thinkexist1989/Smart-Bio-Sensor/Windows/HzBoardDataDisplay/zoomIn.png

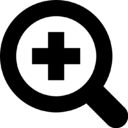
Windows/HzBoardDataDisplay/zoomIn.png
