thinkexist1989/Smart-Bio-Sensor/Firmware/Src/usart.c

/**
  ******************************************************************************
  * File Name          : USART.c
  * Description        : This file provides code for the configuration
  *                      of the USART instances.
  ******************************************************************************
  ** This notice applies to any and all portions of this file
  * that are not between comment pairs USER CODE BEGIN and
  * USER CODE END. Other portions of this file, whether 
  * inserted by the user or by software development tools
  * are owned by their respective copyright owners.
  *
  * COPYRIGHT(c) 2018 STMicroelectronics
  *
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
  ******************************************************************************
  */

/* Includes ------------------------------------------------------------------*/
#include "usart.h"

#include "gpio.h"
#include "dma.h"

/* USER CODE BEGIN 0 */
#include "dac8830.h"

extern double vout[4];
extern int valarray[4];

char RxBuf[256] = {'0'}; //0xff
char TxBuf1[256] = {'0'};
char TxBuf2[256] = {'0'};
uartCtrl uart;
BOOL bUartNewData = FALSE;

/* USER CODE END 0 */

UART_HandleTypeDef huart1;
UART_HandleTypeDef huart2;
DMA_HandleTypeDef hdma_usart1_tx;
DMA_HandleTypeDef hdma_usart2_tx;

/* USART1 init function */

void MX_USART1_UART_Init(void)
{

  huart1.Instance = USART1;
  huart1.Init.BaudRate = 115200;
  huart1.Init.WordLength = UART_WORDLENGTH_8B;
  huart1.Init.StopBits = UART_STOPBITS_1;
  huart1.Init.Parity = UART_PARITY_NONE;
  huart1.Init.Mode = UART_MODE_TX_RX;
  huart1.Init.HwFlowCtl = UART_HWCONTROL_NONE;
  huart1.Init.OverSampling = UART_OVERSAMPLING_16;
  if (HAL_UART_Init(&huart1) != HAL_OK)
  {
    _Error_Handler(__FILE__, __LINE__);
  }

}
/* USART2 init function */

void MX_USART2_UART_Init(void)
{

  huart2.Instance = USART2;
  huart2.Init.BaudRate = 115200;
  huart2.Init.WordLength = UART_WORDLENGTH_8B;
  huart2.Init.StopBits = UART_STOPBITS_1;
  huart2.Init.Parity = UART_PARITY_NONE;
  huart2.Init.Mode = UART_MODE_TX_RX;
  huart2.Init.HwFlowCtl = UART_HWCONTROL_NONE;
  huart2.Init.OverSampling = UART_OVERSAMPLING_16;
  if (HAL_UART_Init(&huart2) != HAL_OK)
  {
    _Error_Handler(__FILE__, __LINE__);
  }

}

void HAL_UART_MspInit(UART_HandleTypeDef* uartHandle)
{

  GPIO_InitTypeDef GPIO_InitStruct;
  if(uartHandle->Instance==USART1)
  {
    /* USART1 clock enable */
    __HAL_RCC_USART1_CLK_ENABLE();
  
    /**USART1 GPIO Configuration    
    PA9     ------> USART1_TX
    PA10     ------> USART1_RX 
    */
    GPIO_InitStruct.Pin = GPIO_PIN_9|GPIO_PIN_10;
    GPIO_InitStruct.Mode = GPIO_MODE_AF_PP;
    GPIO_InitStruct.Pull = GPIO_PULLUP;
    GPIO_InitStruct.Speed = GPIO_SPEED_FREQ_VERY_HIGH;
    GPIO_InitStruct.Alternate = GPIO_AF7_USART1;
    HAL_GPIO_Init(GPIOA, &GPIO_InitStruct);

    /* USART1 DMA Init */
    /* USART1_TX Init */
    hdma_usart1_tx.Instance = DMA2_Stream7;
    hdma_usart1_tx.Init.Channel = DMA_CHANNEL_4;
    hdma_usart1_tx.Init.Direction = DMA_MEMORY_TO_PERIPH;
    hdma_usart1_tx.Init.PeriphInc = DMA_PINC_DISABLE;
    hdma_usart1_tx.Init.MemInc = DMA_MINC_ENABLE;
    hdma_usart1_tx.Init.PeriphDataAlignment = DMA_PDATAALIGN_BYTE;
    hdma_usart1_tx.Init.MemDataAlignment = DMA_MDATAALIGN_BYTE;
    hdma_usart1_tx.Init.Mode = DMA_NORMAL;
    hdma_usart1_tx.Init.Priority = DMA_PRIORITY_LOW;
    hdma_usart1_tx.Init.FIFOMode = DMA_FIFOMODE_DISABLE;
    if (HAL_DMA_Init(&hdma_usart1_tx) != HAL_OK)
    {
      _Error_Handler(__FILE__, __LINE__);
    }

    __HAL_LINKDMA(uartHandle,hdmatx,hdma_usart1_tx);

    /* USART1 interrupt Init */
    HAL_NVIC_SetPriority(USART1_IRQn, 2, 0);
    HAL_NVIC_EnableIRQ(USART1_IRQn);
  }
  else if(uartHandle->Instance==USART2)
  {
    /* USART2 clock enable */
    __HAL_RCC_USART2_CLK_ENABLE();
  
    /**USART2 GPIO Configuration    
    PA2     ------> USART2_TX
    PA3     ------> USART2_RX 
    */
    GPIO_InitStruct.Pin = GPIO_PIN_2|GPIO_PIN_3;
    GPIO_InitStruct.Mode = GPIO_MODE_AF_PP;
    GPIO_InitStruct.Pull = GPIO_PULLUP;
    GPIO_InitStruct.Speed = GPIO_SPEED_FREQ_VERY_HIGH;
    GPIO_InitStruct.Alternate = GPIO_AF7_USART2;
    HAL_GPIO_Init(GPIOA, &GPIO_InitStruct);

    /* USART2 DMA Init */
    /* USART2_TX Init */
    hdma_usart2_tx.Instance = DMA1_Stream6;
    hdma_usart2_tx.Init.Channel = DMA_CHANNEL_4;
    hdma_usart2_tx.Init.Direction = DMA_MEMORY_TO_PERIPH;
    hdma_usart2_tx.Init.PeriphInc = DMA_PINC_DISABLE;
    hdma_usart2_tx.Init.MemInc = DMA_MINC_ENABLE;
    hdma_usart2_tx.Init.PeriphDataAlignment = DMA_PDATAALIGN_BYTE;
    hdma_usart2_tx.Init.MemDataAlignment = DMA_MDATAALIGN_BYTE;
    hdma_usart2_tx.Init.Mode = DMA_NORMAL;
    hdma_usart2_tx.Init.Priority = DMA_PRIORITY_LOW;
    hdma_usart2_tx.Init.FIFOMode = DMA_FIFOMODE_DISABLE;
    if (HAL_DMA_Init(&hdma_usart2_tx) != HAL_OK)
    {
      _Error_Handler(__FILE__, __LINE__);
    }

    __HAL_LINKDMA(uartHandle,hdmatx,hdma_usart2_tx);

    /* USART2 interrupt Init */
    HAL_NVIC_SetPriority(USART2_IRQn, 2, 1);
    HAL_NVIC_EnableIRQ(USART2_IRQn);
  }
}

void HAL_UART_MspDeInit(UART_HandleTypeDef* uartHandle)
{

  if(uartHandle->Instance==USART1)
  {
    /* Peripheral clock disable */
    __HAL_RCC_USART1_CLK_DISABLE();
  
    /**USART1 GPIO Configuration    
    PA9     ------> USART1_TX
    PA10     ------> USART1_RX 
    */
    HAL_GPIO_DeInit(GPIOA, GPIO_PIN_9|GPIO_PIN_10);

    /* USART1 DMA DeInit */
    HAL_DMA_DeInit(uartHandle->hdmatx);

    /* USART1 interrupt Deinit */
    HAL_NVIC_DisableIRQ(USART1_IRQn);
  }
  else if(uartHandle->Instance==USART2)
  {
    /* Peripheral clock disable */
    __HAL_RCC_USART2_CLK_DISABLE();
  
    /**USART2 GPIO Configuration    
    PA2     ------> USART2_TX
    PA3     ------> USART2_RX 
    */
    HAL_GPIO_DeInit(GPIOA, GPIO_PIN_2|GPIO_PIN_3);

    /* USART2 DMA DeInit */
    HAL_DMA_DeInit(uartHandle->hdmatx);

    /* USART2 interrupt Deinit */
    HAL_NVIC_DisableIRQ(USART2_IRQn);
  }
} 

/* USER CODE BEGIN 1 */

/******printf重定向函数******/
#ifdef __GNUC__
  /* With GCC/RAISONANCE, small printf (option LD Linker->Libraries->Small printf
     set to 'Yes') calls __io_putchar() */
  #define PUTCHAR_PROTOTYPE int __io_putchar(int ch)
#else
  #define PUTCHAR_PROTOTYPE int fputc(int ch, FILE *f)
#endif /* __GNUC__ */
/**
  * @brief  Retargets the C library printf function to the USART.
  * @param  None
  * @retval None
  */
PUTCHAR_PROTOTYPE
{
  /* Place your implementation of fputc here */
  /* e.g. write a character to the EVAL_COM1 and Loop until the end of transmission */
  HAL_UART_Transmit(&huart1, (uint8_t *)&ch, 1, 0xFFFF);
  //HAL_UART_Transmit_DMA(&huart1, (uint8_t *)&ch, 1);
  return ch;
}


/******串口中断处理回调函数*******/
void HAL_UART_RxCpltCallback(UART_HandleTypeDef *huart)
{
  UNUSED(huart); //防止某些编译器出错
	
	if(huart == &huart1){	
		uart.iRxPtr = (uart.iRxPtr + 1)&0xFF; //环形缓冲区处理
		bUartNewData = TRUE;
		//dataFrame_OK(&uart, RxBuf);
	
		HAL_UART_Receive_IT(&huart1, (uint8_t *)(&RxBuf[uart.iRxPtr]), 1);
	}
}

void HAL_UART_TxCpltCallback(UART_HandleTypeDef *huart)
{
	UNUSED(huart); //防止某些编译器出错
	
	if(huart == &huart1){	
		uart.bSended1 = TRUE;
	}
	else if(huart == &huart2){
		uart.bSended2 = TRUE;
	}
}  


/******串口数据帧解析函数********/
void dataFrame_OK(uartCtrl* pUart, char* pBuf)
{
	while(pUart->iGetPtr != pUart->iRxPtr){
		if(pUart->iOrder == 0)
		{
			if(pBuf[pUart->iGetPtr] == 'v'){
				pUart->iOrder = VOUT;
				pUart->iEndPtr = (pUart->iGetPtr+1)&0xFF;
			}
			else if(pBuf[pUart->iGetPtr] == 'n'){
				pUart->iOrder = VALOUT;
				pUart->iEndPtr = (pUart->iGetPtr+1)&0xFF;
			}
			else if(pBuf[pUart->iGetPtr] == 'd'){
				pUart->iOrder = DACSET;
				pUart->iEndPtr = (pUart->iGetPtr+4)&0xFF;
			}
		}
		else{
			if(pUart->iGetPtr == pUart->iEndPtr){
				switch(pUart->iOrder){
					case VOUT:
						switch(pBuf[pUart->iGetPtr]){
							case '1':
								printf("%f\n", vout[0]);
								break;
							case '2':
								printf("%f\n", vout[1]);
								break;
							case '3':
								printf("%f\n", vout[2]);
								break;
							case '4':
								printf("%f\n", vout[3]);
								break;
							case '5':
							{
								memcpy(TxBuf1,'\0',256);
								sprintf((char*)TxBuf1,"Vout1: %f, Vout2: %f, Vout3: %f, Vout4: %f\n", vout[0],vout[1],vout[2],vout[3]);
								HAL_UART_Transmit_DMA(&huart1,TxBuf1,strlen(TxBuf1));
								//HAL_UART_Transmit_DMA(&huart1,tempbuf,100);
								//printf("Vout1: %f, Vout2: %f, Vout3: %f, Vout4: %f\n", vout[0],vout[1],vout[2],vout[3]);															
								break;
							}
							default: break;
						}
						break;
					case VALOUT:
						switch(pBuf[pUart->iGetPtr]){
							case '1':
								printf("%x\n", valarray[0]);
								break;
							case '2':
								printf("%x\n", valarray[1]);
								break;
							case '3':
								printf("%x\n", valarray[2]);
								break;
							case '4':
								printf("%x\n", valarray[3]);
								break;
							case '5':
								printf("Val1: %x, Val2: %x, Val3: %x, Val4: %x\n", valarray[0],valarray[1],valarray[2],valarray[3]);
								break;
							default: break;
						}
						break;
					case DACSET:{
						char buf[5];
						buf[0] = pBuf[(pUart->iGetPtr-3)&0xFF];buf[1] = pBuf[(pUart->iGetPtr-2)&0xFF];buf[2] = pBuf[(pUart->iGetPtr-1)&0xFF];buf[3] = pBuf[(pUart->iGetPtr-0)&0xFF];buf[4] = '\n';
						iDacMv = atoi(buf);
						DAC_SetVout(iDacMv);
						printf("DAC output is: %d mv\n",iDacMv);
					}
						break;
					default: break;
				}
				pUart->iOrder = 0;
			}
		}
		pUart->iGetPtr = (pUart->iGetPtr+1)&0xFF;
	}
}


/* USER CODE END 1 */

/**
  * @}
  */

/**
  * @}
  */

/************************ (C) COPYRIGHT STMicroelectronics *****END OF FILE****/
